Tomvhattem/8P370_UC2_Hardware/UC2/Mechanical_Z-Stage/Base.stl

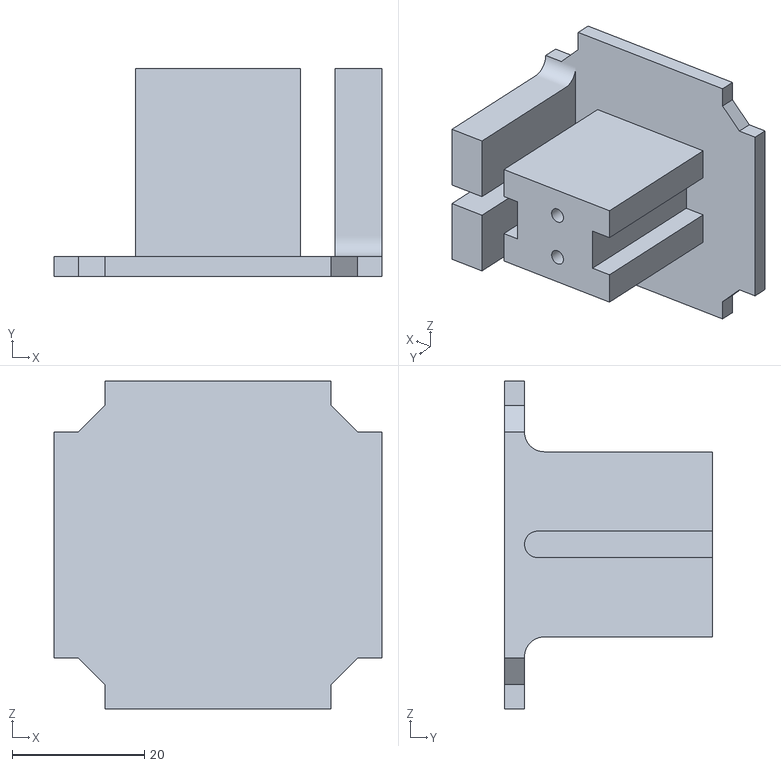
[picture p22: CAD file, 2023-10-17]
UC2/Mechanical_Z-Stage/Base.stl
49.6 x 31.4 x 49.6
