Tomvhattem/8P370_UC2_Hardware/OpenFlexure/STL/Motorized/delta_stage_remaster.stl

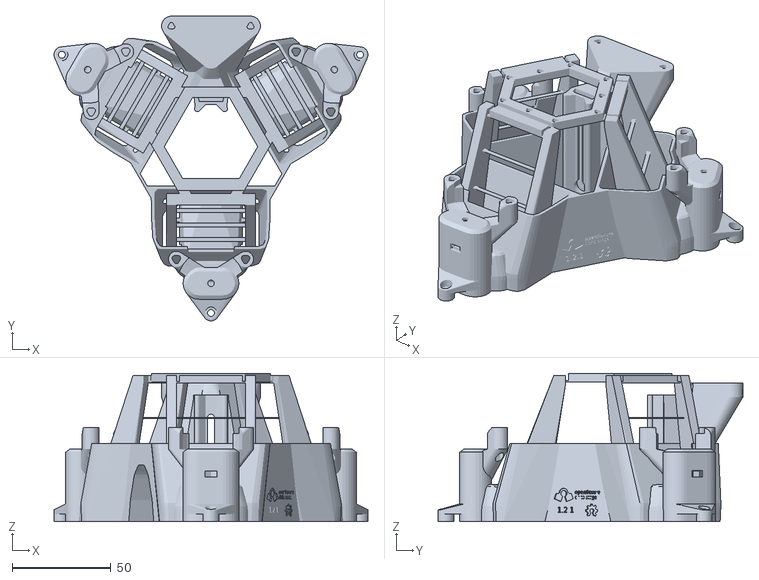
[picture p23: CAD file, 2023-10-17]
OpenFlexure/STL/Motorized/delta_stage_remaster.stl
158.7 x 154.0 x 75.0
