Tomvhattem/8P370_UC2_Hardware/OpenFlexure/STL/Optional/OPTIONAL_sample_clips.stl

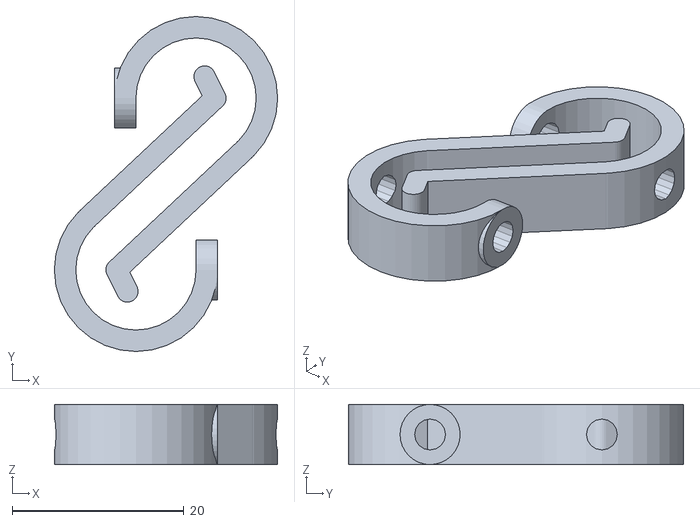
[picture p24: CAD file, 2023-10-17]
OpenFlexure/STL/Optional/OPTIONAL_sample_clips.stl
26.0 x 39.0 x 7.00
