Tomvhattem/8P370_UC2_Hardware/OpenFlexure/STL/Mechanical/feet_lowprofile_UC2.stl

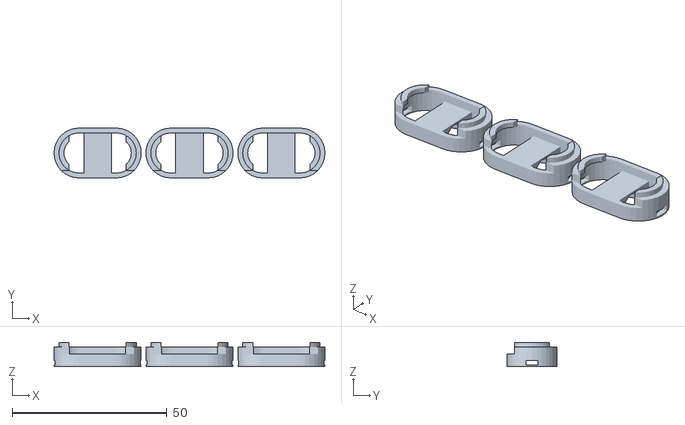
[picture p25: CAD file, 2023-10-17]
OpenFlexure/STL/Mechanical/feet_lowprofile_UC2.stl
87.6 x 16.1 x 7.84
