Tomvhattem/8P370_UC2_Hardware/UC2/Mechanical_Z-Stage/FineAdjustments2.stl

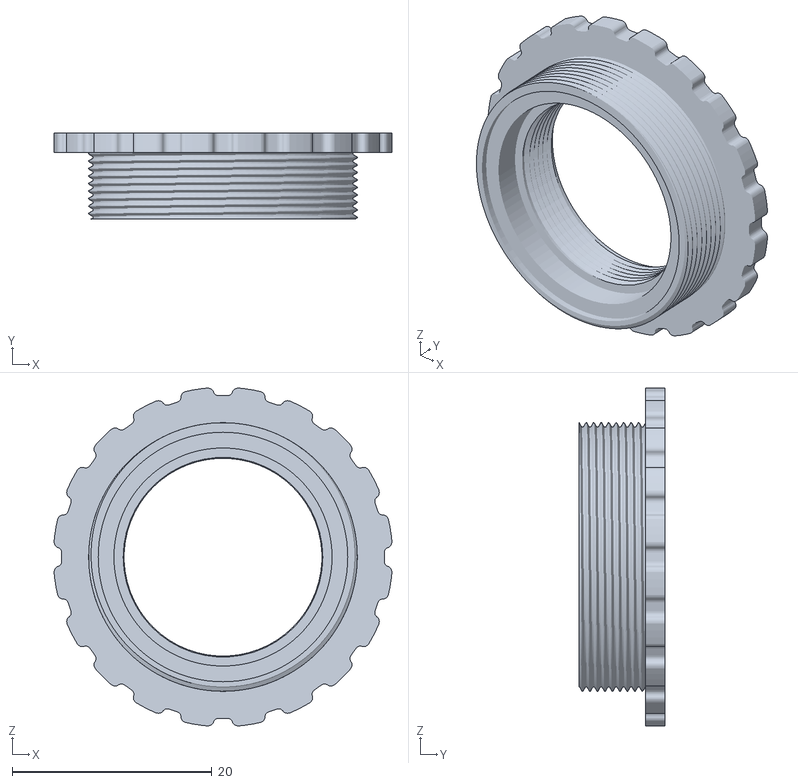
[picture p26: CAD file, 2023-10-17]
UC2/Mechanical_Z-Stage/FineAdjustments2.stl
33.9 x 8.66 x 33.9
