Tomvhattem/8P370_UC2_Hardware/OpenFlexure/STL/Motorized/small_gears.stl

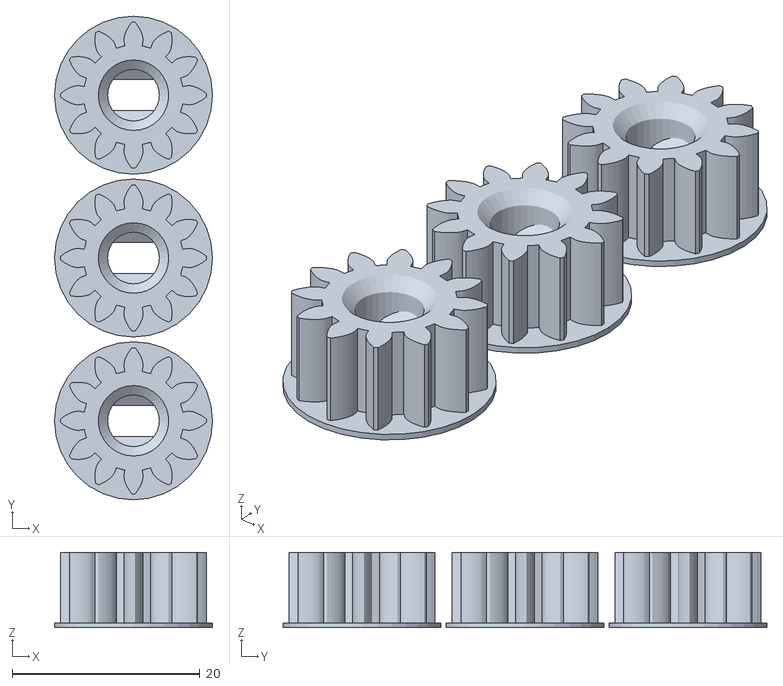
[picture p27: CAD file, 2023-10-17]
OpenFlexure/STL/Motorized/small_gears.stl
16.8 x 51.5 x 8.00
