Tomvhattem/8P370_UC2_Hardware/OpenFlexure/STL/Motorized/large_gears.stl

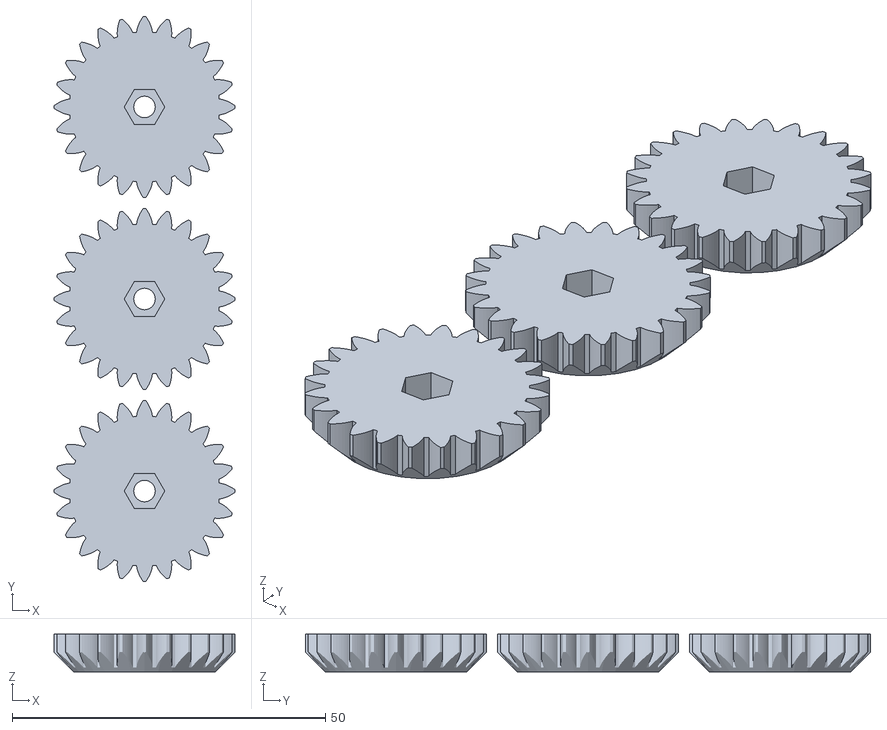
[picture p28: CAD file, 2023-10-17]
OpenFlexure/STL/Motorized/large_gears.stl
28.9 x 90.2 x 6.00
